MaxLell/Pomodoro_Clock/Documentation/Git Work Flow/Pomodoro Git Flow.drawio(1).png

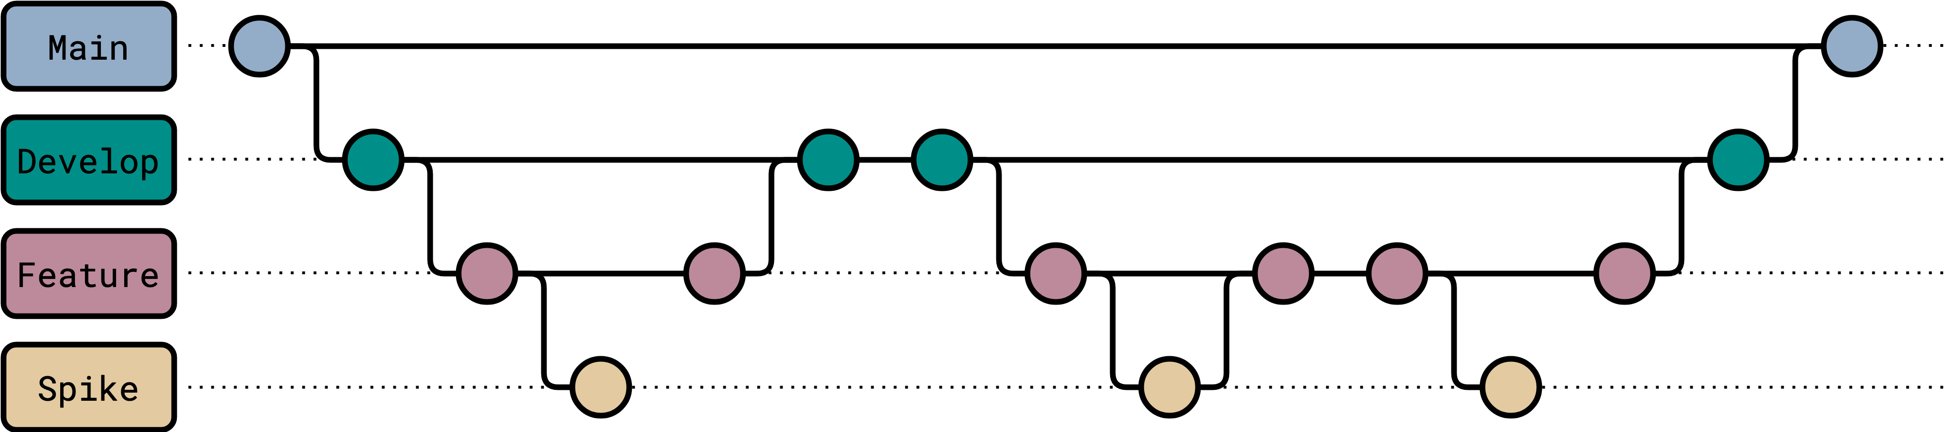
Documentation/Git Work Flow/Pomodoro Git Flow.drawio(1).png
