MaxLell/Pomodoro_Clock/Software/Firmware/G071_Pomodoro_Prototype/Core/Inc/main.h

#define TRIGGER_BTN_Pin GPIO_PIN_13
#define TRIGGER_BTN_GPIO_Port GPIOC
#define NRST_Pin GPIO_PIN_2
#define NRST_GPIO_Port GPIOF
#define ENCODER_BTN_Pin GPIO_PIN_3
#define ENCODER_BTN_GPIO_Port GPIOC
#define ENCODER_A_Pin GPIO_PIN_0
#define ENCODER_A_GPIO_Port GPIOA
#define ENCODER_B_Pin GPIO_PIN_1
#define ENCODER_B_GPIO_Port GPIOA
#define USART2_TX_Pin GPIO_PIN_2
#define USART2_TX_GPIO_Port GPIOA
#define USART2_RX_Pin GPIO_PIN_3
#define USART2_RX_GPIO_Port GPIOA
#define BLINKY_LED_Pin GPIO_PIN_5
#define BLINKY_LED_GPIO_Port GPIOA
#define RGB_LED_Pin GPIO_PIN_8
#define RGB_LED_GPIO_Port GPIOA
#define GPIO_Output_Pin GPIO_PIN_7
#define GPIO_Output_GPIO_Port GPIOC
#define GPIO_OutputD9_Pin GPIO_PIN_9
#define GPIO_OutputD9_GPIO_Port GPIOD
#define SWDIO_Pin GPIO_PIN_13
#define SWDIO_GPIO_Port GPIOA
#define SWCLK_Pin GPIO_PIN_14
#define SWCLK_GPIO_Port GPIOA
#define GPIO_OutputD5_Pin GPIO_PIN_5
#define GPIO_OutputD5_GPIO_Port GPIOD
#define GPIO_OutputD6_Pin GPIO_PIN_6
#define GPIO_OutputD6_GPIO_Port GPIOD
#define I2C1_SCL_Pin GPIO_PIN_6
#define I2C1_SCL_GPIO_Port GPIOB
#define I2C1_SDA_Pin GPIO_PIN_7
#define I2C1_SDA_GPIO_Port GPIOB
