MaxLell/Pomodoro_Clock/Software/Firmware/G071_Pomodoro_Prototype/User/PomodoroControl/PomodoroControl.h

#ifndef POMODOROCONTROL_H
#define POMODOROCONTROL_H

#include "Common.h"
#include "PomodoroControl_Datatypes.h"

typedef struct
{
    uint8_t u8Worktime;
    uint8_t u8Breaktime;
    uint8_t au8MinuteArray[TOTAL_MINUTES];
} PCTRL_Progress_t;

typedef struct
{
    uint16_t u16DurationPerIncrementMsec;
    uint8_t u8FillingMin;
    int8_t i8Animation;
    BOOL bIsComplete;
    BOOL bIsTimerInitialized;
} PCTRL_RingCountdown_t;

void PomodoroControl_init(void);

status_e PomodoroControl_execute(void);

#endif // POMODOROCONTROL_H
