MaxLell/Pomodoro_Clock/Software/Firmware/G071_Pomodoro_Prototype/Core/Inc/RgbLed.h

/*
 * RgbLed.h
 *
 *  Created on: Nov 29, 2023
 *      Author: maxlell
 */

#ifndef RGBLED_H_
#define RGBLED_H_

#include "stdint.h"

#define RGB_LED_TOTAL_LEDS 24

void RgbLed_show(void);

void RgbLed_setPixelColor(
    uint8_t ledIndex,
    uint8_t u8Red, uint8_t u8Green, uint8_t u8Blue);

void RgbLed_isr();

void RgbLed_testDrawSpinningCircle();

#endif /* RGBLED_H_ */
