MaxLell/Pomodoro_Clock/Software/Firmware/L476_Pomodoro_App/Bsp/Led/BlinkyLed.c

#include "BlinkyLed.h"

#include "Common.h"
#include "stm32l476xx.h"
#include "RegisterAccess.h"

/**
 * The LED blinky LED is connected to PA5
 */

void BlinkyLed_init(void)
{
    /* Turn on the Clock for GPIOA */
    RCC->AHB2ENR |= RCC_AHB2ENR_GPIOAEN;

    /* Set PA5 to output Mode */
    GPIOA->MODER &= ~GPIO_MODER_MODE5_1;
    GPIOA->MODER |= GPIO_MODER_MODE5_0;
}

void BlinkyLed_enable(void)
{
    /* set HIGH value on pin PA5 */
    GPIOA->BSRR |= GPIO_BSRR_BS_5;
}
void BlinkyLed_disable(void)
{
    /* set LOW value on pin PA5 */
    GPIOA->BSRR |= GPIO_BSRR_BR_5;
}

void BlinkyLed_toggle(void)
{
    /**
     * This reads in the 5th register of PortA -> PA5
     * This is the same pin, to which the LED is attached
     * to
     */
    if ((GPIOA->IDR & (1 << 5)))
    {
        /**
         * When the LED was on: Switch it off.
         */
        BlinkyLed_disable();
    }
    else
    {
        /**
         * When the LED was off: Switch it on.
         */
        /**
         * Setting the LED, changes the value that is read
         * on the Input Data Register
         */
        BlinkyLed_enable();
    }
}
